bagatraya/Buffered-Dual-Loop-Station-Pedal/Buffered-Dual-Loop-Station-Pedal/Documentation/1.jpg

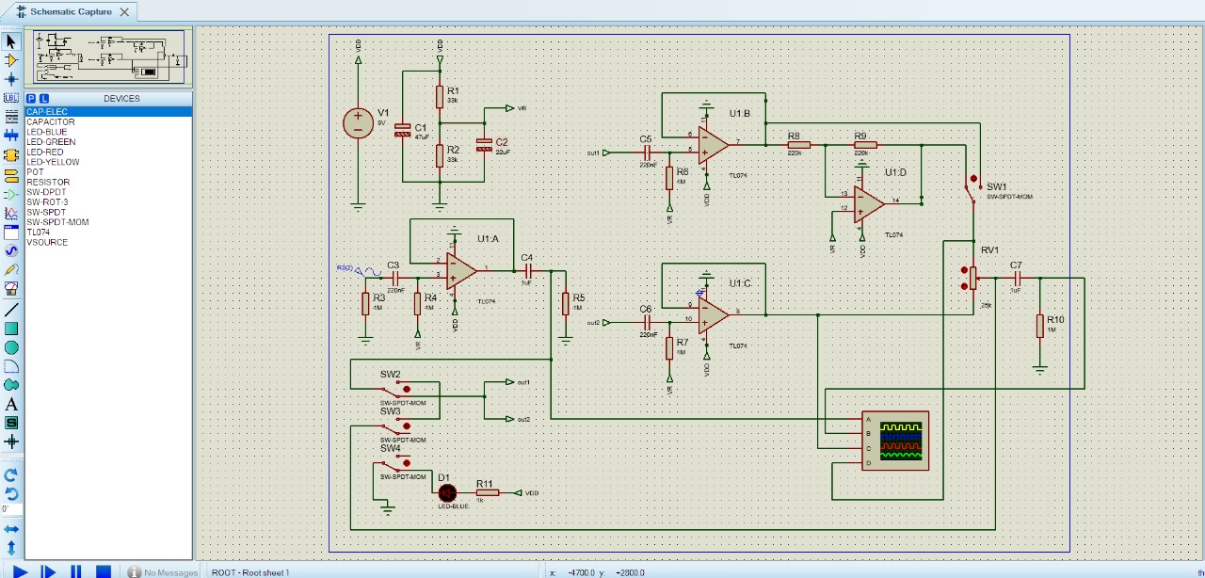
Buffered-Dual-Loop-Station-Pedal/Documentation/1.jpg
