bagatraya/Buffered-Dual-Loop-Station-Pedal/Buffered-Dual-Loop-Station-Pedal/Documentation/2.jpg

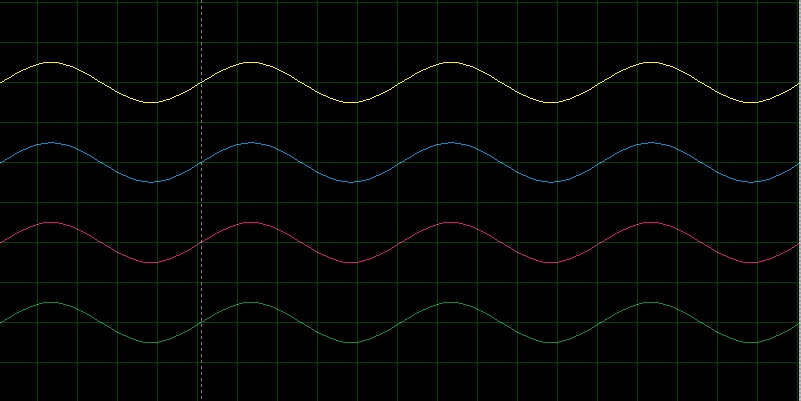
Buffered-Dual-Loop-Station-Pedal/Documentation/2.jpg
