bagatraya/Buffered-Dual-Loop-Station-Pedal/Buffered-Dual-Loop-Station-Pedal/Documentation/3.jpg

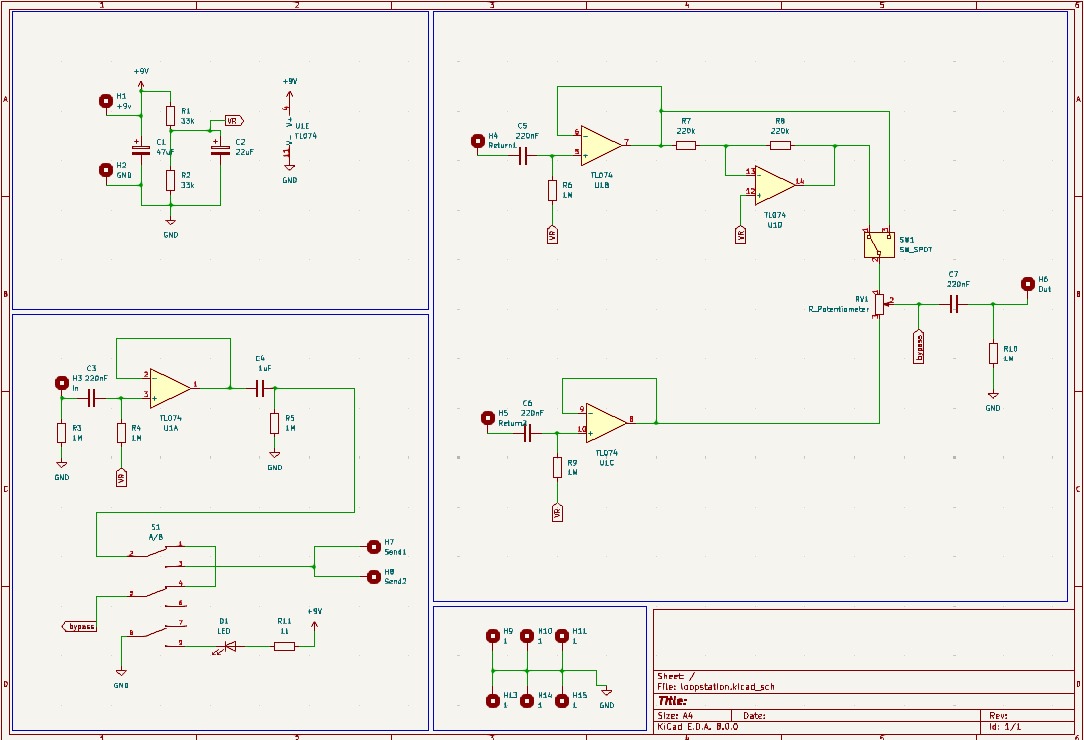
Buffered-Dual-Loop-Station-Pedal/Documentation/3.jpg
