bagatraya/Buffered-Dual-Loop-Station-Pedal/Buffered-Dual-Loop-Station-Pedal/Documentation/4.jpg

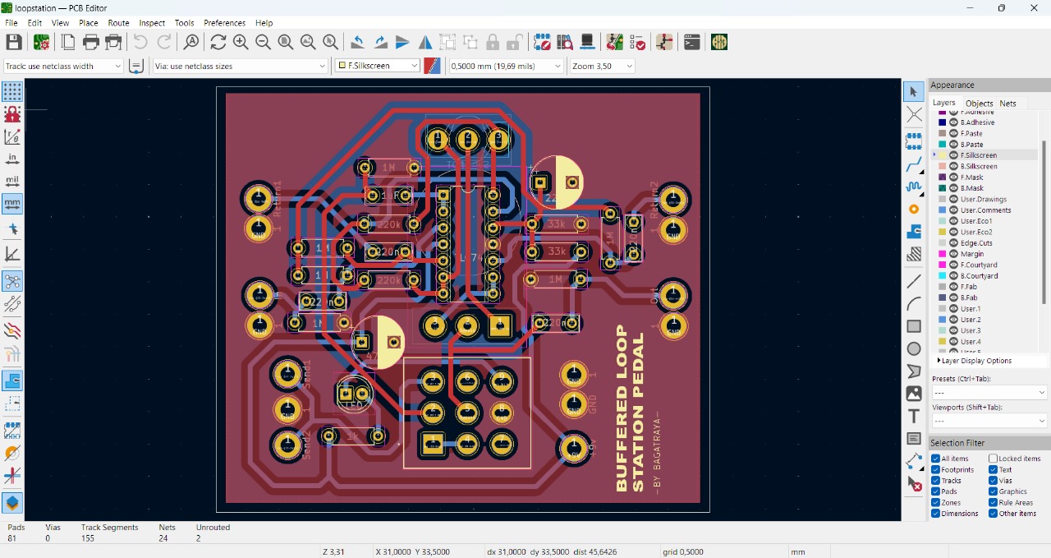
Buffered-Dual-Loop-Station-Pedal/Documentation/4.jpg
