bagatraya/Buffered-Dual-Loop-Station-Pedal/Buffered-Dual-Loop-Station-Pedal/Documentation/7.jpg

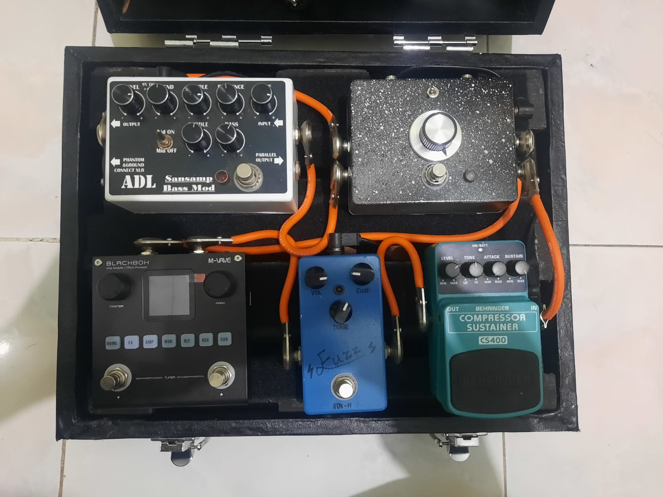
Buffered-Dual-Loop-Station-Pedal/Documentation/7.jpg
