bagatraya/Buffered-Dual-Loop-Station-Pedal/Buffered-Dual-Loop-Station-Pedal/kicad/PCB/revisi2/loopstation-B_Silkscreen.pdf

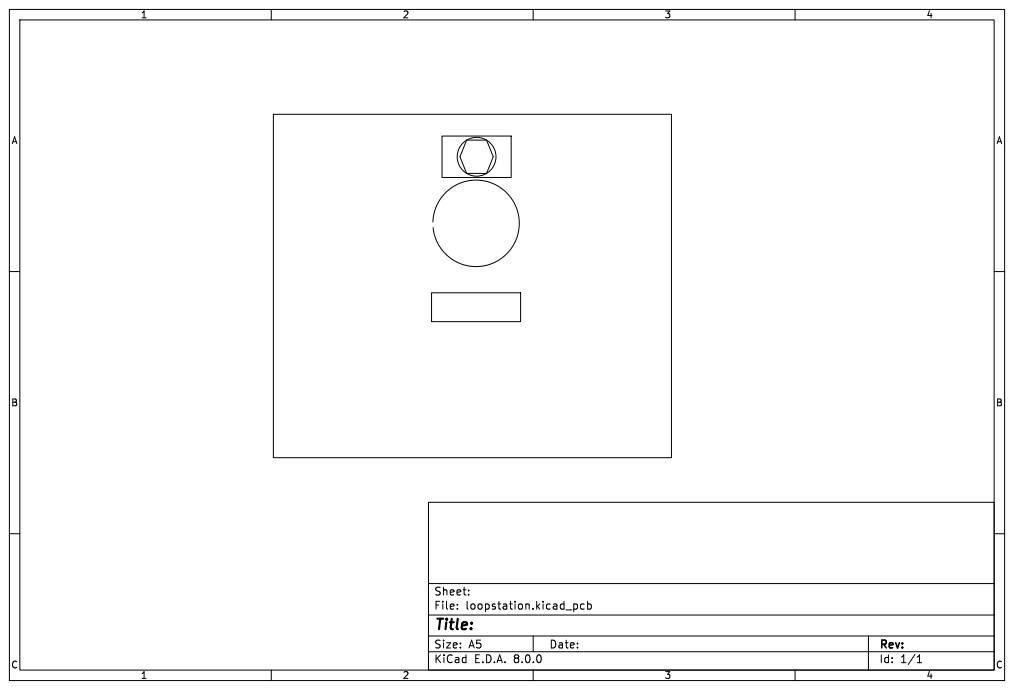
[picture p15: page 1]

Id: 1/1 Title: File: loopstation.kicad_pcb Sheet:
