bagatraya/Buffered-Dual-Loop-Station-Pedal/Buffered-Dual-Loop-Station-Pedal/kicad/PCB/revisi2/loopstation-F_Mask.pdf

Id: 1/1 Title: File: loopstation.kicad_pcb Sheet:
